stefy-d/ebook_reader_tsc/Images/2025-04-02 112556.png

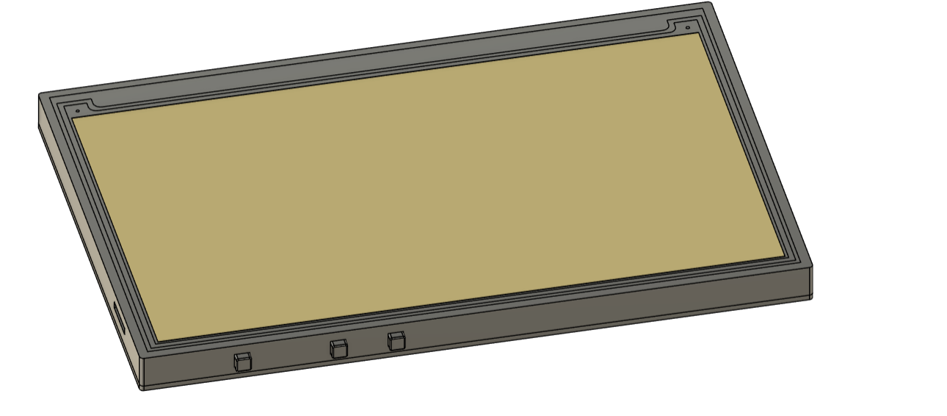
Images/2025-04-02 112556.png
