stefy-d/ebook_reader_tsc/Images/2025-04-02 160916.png

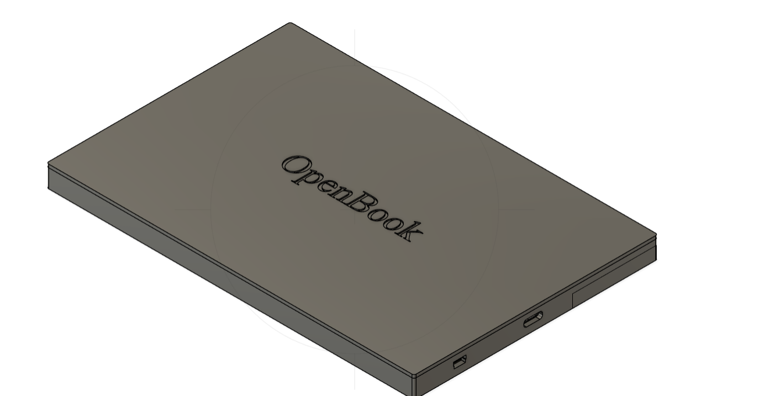
Images/2025-04-02 160916.png
